djvs/nec-pc-8801-linear/IMG_20210819_163000.jpg

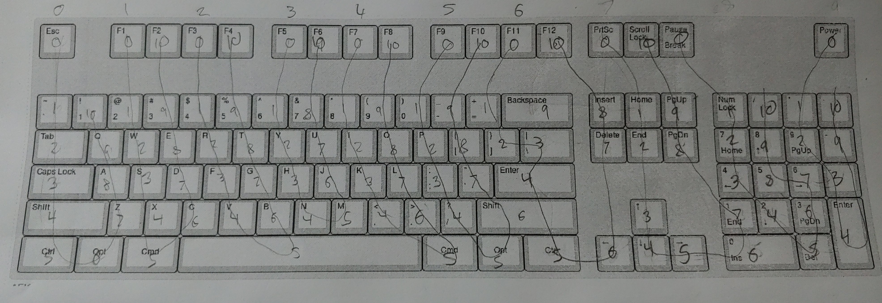
IMG_20210819_163000.jpg
