djvs/nec-pc-8801-linear/necpc8801l.kicad_sch

## KiCad design necpc8801l.kicad_sch (2022-12-16)

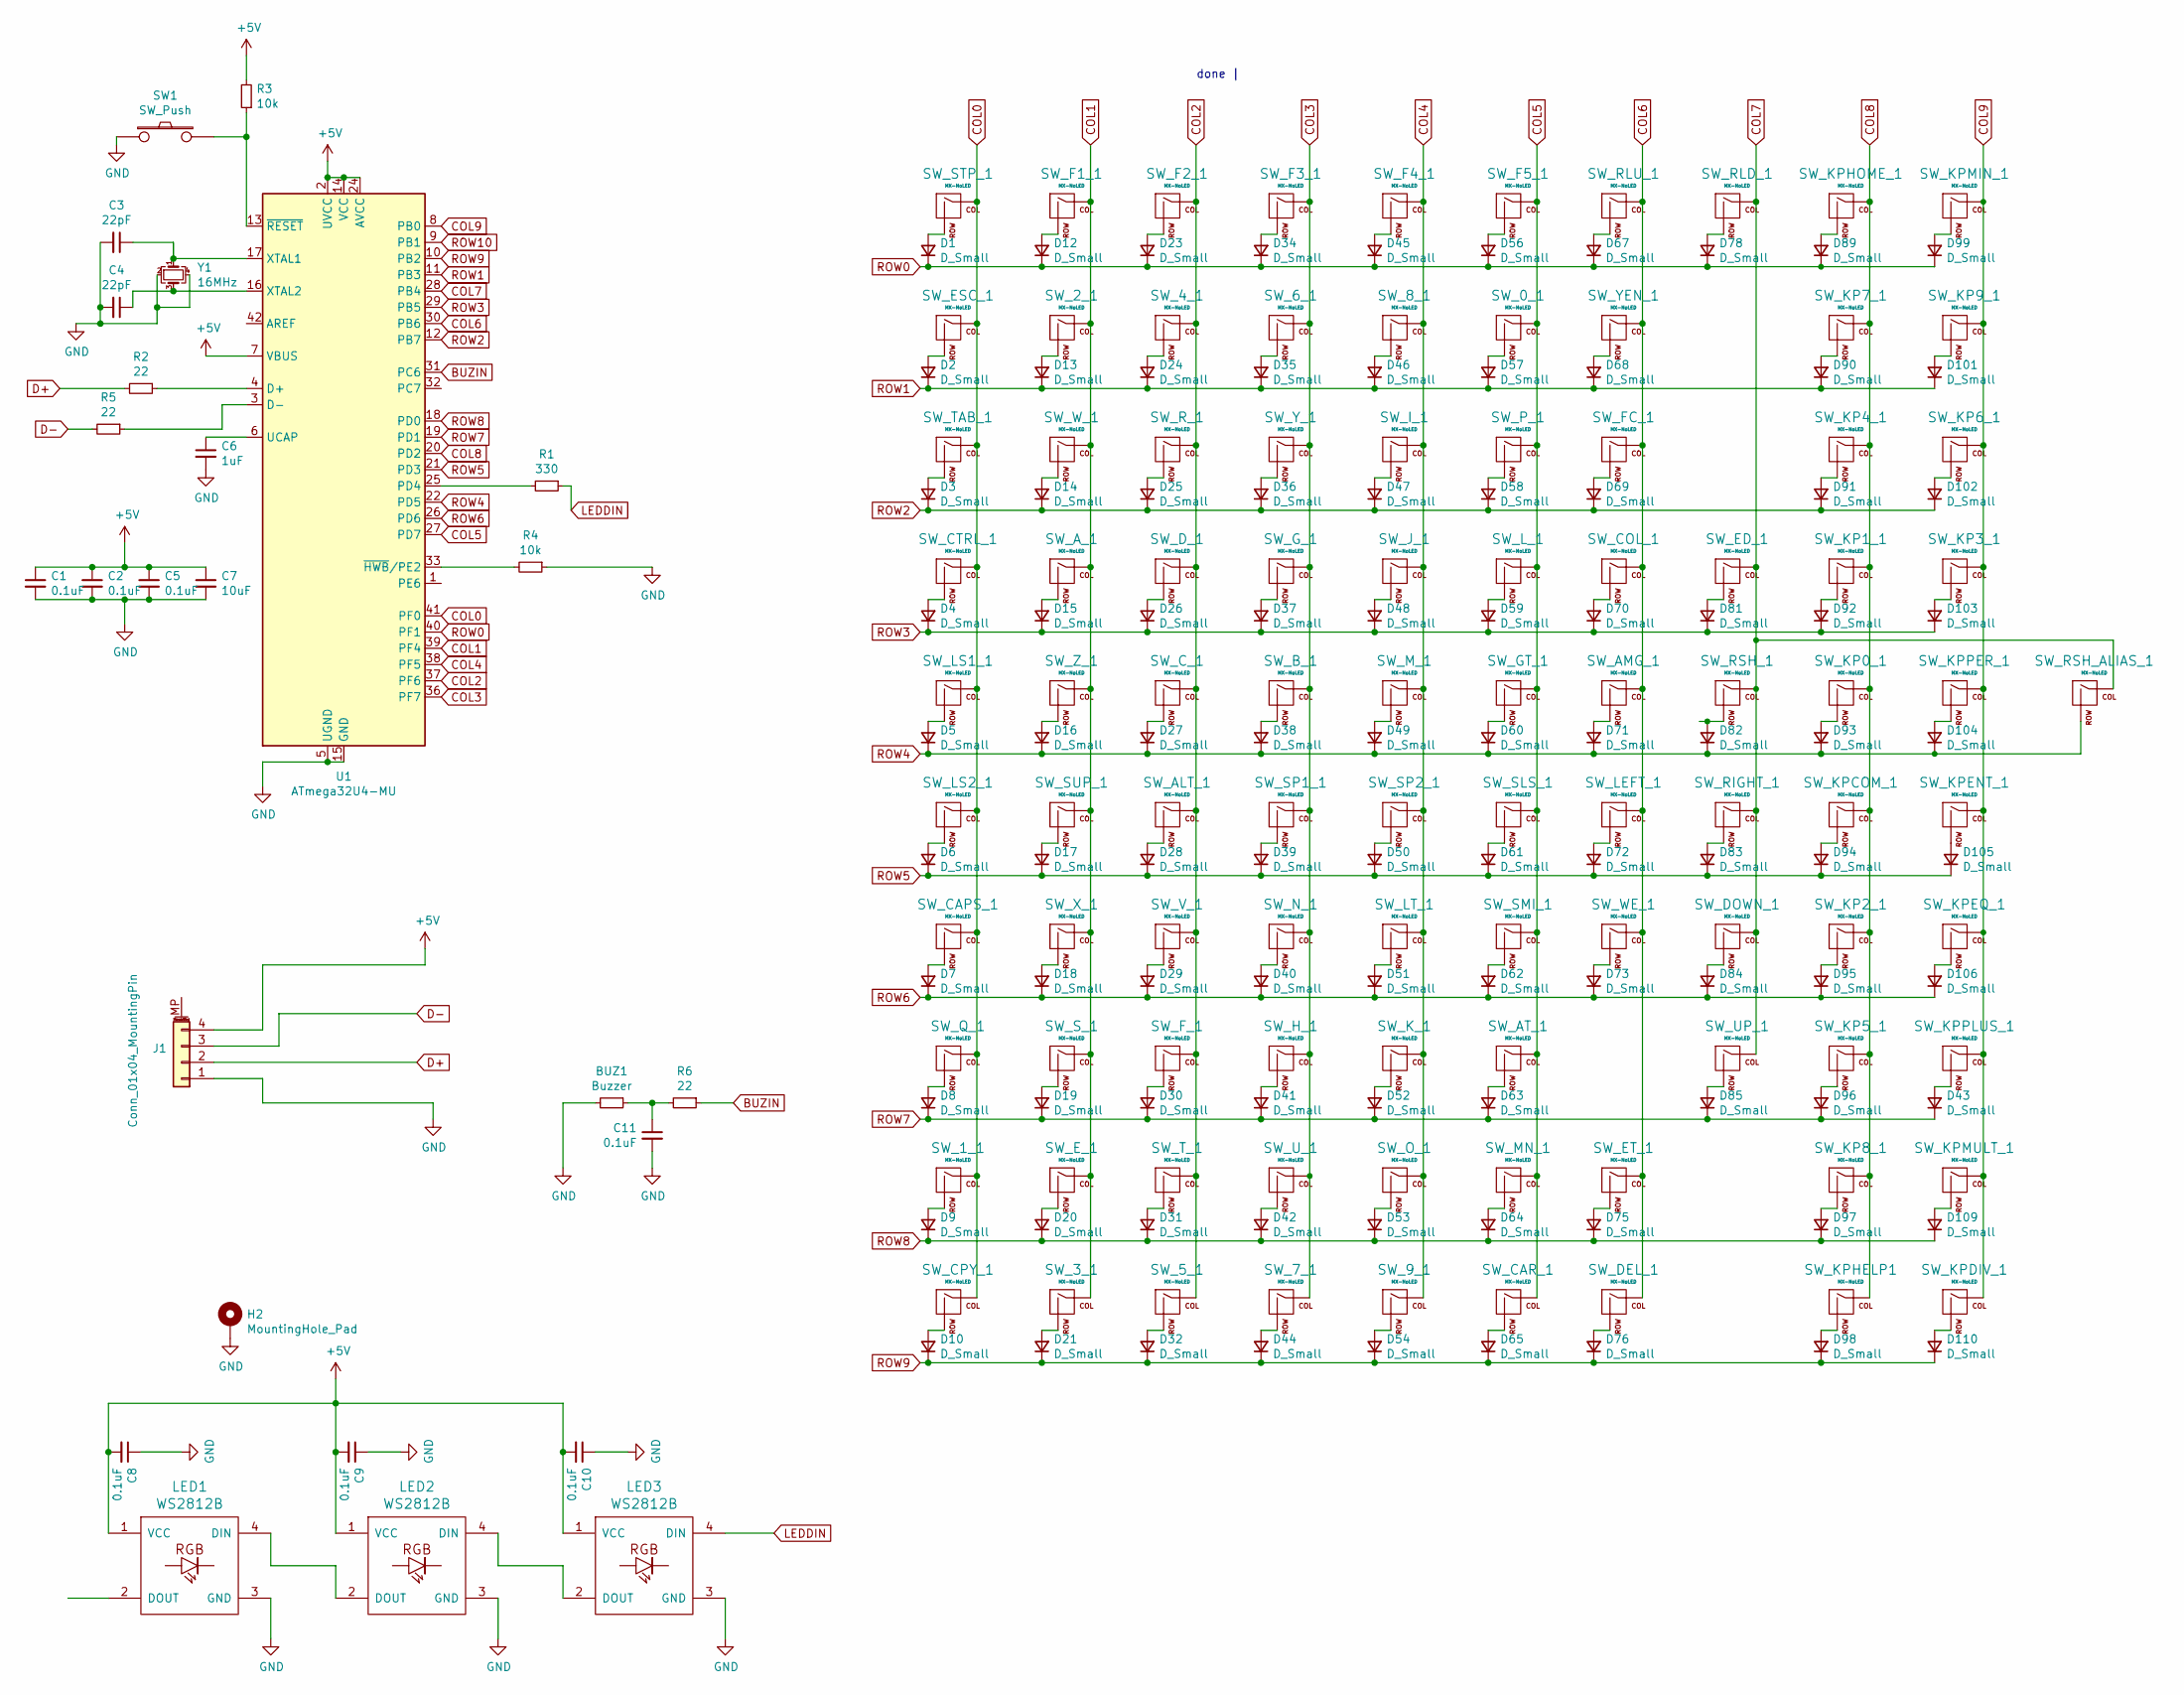
[picture p9: schematic necpc8801l.kicad_sch]

Parts:
BUZ1: Buzzer; Buzzer_Mallory_AST1109MLTRQ
C1, C2, C5, C8, C9, C10, C11: 0.1uF; C_0805_2012Metric
C3, C4: 22pF; C_0805_2012Metric
C6: 1uF; C_0805_2012Metric
C7: 10uF; C_0805_2012Metric
D1, D2, D3, D4, D5, D6, D7, D8, D9, D10, D12, D13, D14, D15, D16, D17, D18, D19, D20, D21, D23, D24, D25, D26, D27, D28, D29, D30, D31, D32, D34, D35, D36, D37, D38, D39, D40, D41, D42, D43, D44, D45, D46, D47, D48, D49, D50, D51, D52, D53, D54, D56, D57, D58, D59, D60, D61, D62, D63, D64, D65, D67, D68, D69, D70, D71, D72, D73, D75, D76, D78, D81, D82, D83, D84, D85, D89, D90, D91, D92, D93, D94, D95, D96, D97, D98, D99, D101, D102, D103, D104, D105, D106, D109, D110: D_Small; D_SOD-123
H2: MountingHole_Pad; MountingHole_2.7mm_M2.5_Pad
J1: Conn_01x04_MountingPin; JST_SH_SM04B-SRSS-TB_1x04-1MP_P1.00mm_Horizontal
LED1, LED2, LED3: WS2812B; WS2812BDual
R1: 330; R_0805_2012Metric
R2, R5, R6: 22; R_0805_2012Metric
R3, R4: 10k; R_0805_2012Metric
SW1: SW_Push; SKQG-1155865
SW_0_1, SW_1_1, SW_2_1, SW_3_1, SW_4_1, SW_5_1, SW_6_1, SW_7_1, SW_8_1, SW_9_1: MX-NoLED; mx-nec-alps
SW_ALT_1: MX-NoLED; mx-nec-alps
SW_AMG_1: MX-NoLED; mx-nec-alps
SW_AT_1: MX-NoLED; mx-nec-alps
SW_A_1: MX-NoLED; mx-nec-alps
SW_B_1: MX-NoLED; mx-nec-alps
SW_CAPS_1: MX-NoLED; mx-nec-alps
SW_CAR_1: MX-NoLED; mx-nec-alps
SW_COL_1: MX-NoLED; mx-nec-alps
SW_CPY_1: MX-NoLED; mx-nec-alps
SW_CTRL_1: MX-NoLED; mx-nec-alps
SW_C_1: MX-NoLED; mx-nec-alps
SW_DEL_1: MX-NoLED; mx-nec-alps
SW_DOWN_1: MX-NoLED; mx-nec-alps
SW_D_1: MX-NoLED; mx-nec-alps
SW_ED_1: MX-NoLED; mx-nec-alps
SW_ESC_1: MX-NoLED; mx-nec-alps
SW_ET_1: MX-NoLED; mx-nec-alps
SW_E_1: MX-NoLED; mx-nec-alps
SW_F1_1, SW_F2_1, SW_F3_1, SW_F4_1, SW_F5_1: MX-NoLED; mx-nec-alps
SW_FC_1: MX-NoLED; mx-nec-alps
SW_F_1: MX-NoLED; mx-nec-alps
SW_GT_1: MX-NoLED; mx-nec-alps
SW_G_1: MX-NoLED; mx-nec-alps
SW_H_1: MX-NoLED; mx-nec-alps
SW_I_1: MX-NoLED; mx-nec-alps
SW_J_1: MX-NoLED; mx-nec-alps
SW_KP0_1, SW_KP1_1, SW_KP2_1, SW_KP3_1, SW_KP4_1, SW_KP5_1, SW_KP6_1, SW_KP7_1, SW_KP8_1, SW_KP9_1: MX-NoLED; mx-nec-alps
SW_KPCOM_1: MX-NoLED; mx-nec-alps
SW_KPDIV_1: MX-NoLED; mx-nec-alps
SW_KPENT_1: MX-NoLED; mx-nec-alps
SW_KPEQ_1: MX-NoLED; mx-nec-alps
SW_KPHELP1: MX-NoLED; mx-nec-alps
SW_KPHOME_1: MX-NoLED; mx-nec-alps
SW_KPMIN_1: MX-NoLED; mx-nec-alps
SW_KPMULT_1: MX-NoLED; mx-nec-alps
SW_KPPER_1: MX-NoLED; mx-nec-alps
SW_KPPLUS_1: MX-NoLED; mx-nec-alps
SW_K_1: MX-NoLED; mx-nec-alps
SW_LEFT_1: MX-NoLED; mx-nec-alps
SW_LS1_1, SW_LS2_1: MX-NoLED; mx-nec-alps
SW_LT_1: MX-NoLED; mx-nec-alps
SW_L_1: MX-NoLED; mx-nec-alps
SW_MN_1: MX-NoLED; mx-nec-alps
SW_M_1: MX-NoLED; mx-nec-alps
SW_N_1: MX-NoLED; mx-nec-alps
SW_O_1: MX-NoLED; mx-nec-alps
SW_P_1: MX-NoLED; mx-nec-alps
SW_Q_1: MX-NoLED; mx-nec-alps
SW_RIGHT_1: MX-NoLED; mx-nec-alps
SW_RLD_1: MX-NoLED; mx-nec-alps
SW_RLU_1: MX-NoLED; mx-nec-alps
SW_RSH_1: MX-NoLED; mx-nec-alps
SW_RSH_ALIAS_1: MX-NoLED; mx-nec-alps
SW_R_1: MX-NoLED; mx-nec-alps
SW_SLS_1: MX-NoLED; mx-nec-alps
SW_SMI_1: MX-NoLED; mx-nec-alps
SW_SP1_1, SW_SP2_1: MX-NoLED; mx-nec-alps
SW_STP_1: MX-NoLED; mx-nec-alps
SW_SUP_1: MX-NoLED; mx-nec-alps
SW_S_1: MX-NoLED; mx-nec-alps
SW_TAB_1: MX-NoLED; mx-nec-alps
SW_T_1: MX-NoLED; mx-nec-alps
SW_UP_1: MX-NoLED; mx-nec-alps
SW_U_1: MX-NoLED; mx-nec-alps
SW_V_1: MX-NoLED; mx-nec-alps
SW_WE_1: MX-NoLED; mx-nec-alps
SW_W_1: MX-NoLED; mx-nec-alps
SW_X_1: MX-NoLED; mx-nec-alps
SW_YEN_1: MX-NoLED; mx-nec-alps
SW_Y_1: MX-NoLED; mx-nec-alps
SW_Z_1: MX-NoLED; mx-nec-alps
U1: ATmega32U4-MU; atmega32u4-mu-and-au
Y1: 16MHz; Crystal_SMD_3225-4Pin_3.2x2.5mm

Connections:
+5V: C1.1, C2.1, C5.1, C7.1, C8.2, C9.2, C10.2, J1.4, LED1.1 (VCC), LED2.1 (VCC), LED3.1 (VCC), R3.2, U1.2 (UVCC), U1.7 (VBUS), U1.14 (VCC), U1.24 (AVCC), U1.34 (VCC), U1.44 (AVCC)
BUZIN: R6.1, U1.31 (PC6)
COL0: SW_1_1.1 (COL), SW_CAPS_1.1 (COL), SW_CPY_1.1 (COL), SW_CTRL_1.1 (COL), SW_ESC_1.1 (COL), SW_LS1_1.1 (COL), SW_LS2_1.1 (COL), SW_Q_1.1 (COL), SW_STP_1.1 (COL), SW_TAB_1.1 (COL), U1.41 (PF0)
COL1: SW_2_1.1 (COL), SW_3_1.1 (COL), SW_A_1.1 (COL), SW_E_1.1 (COL), SW_F1_1.1 (COL), SW_SUP_1.1 (COL), SW_S_1.1 (COL), SW_W_1.1 (COL), SW_X_1.1 (COL), SW_Z_1.1 (COL), U1.39 (PF4)
COL2: SW_4_1.1 (COL), SW_5_1.1 (COL), SW_ALT_1.1 (COL), SW_C_1.1 (COL), SW_D_1.1 (COL), SW_F2_1.1 (COL), SW_F_1.1 (COL), SW_R_1.1 (COL), SW_T_1.1 (COL), SW_V_1.1 (COL), U1.37 (PF6)
COL3: SW_6_1.1 (COL), SW_7_1.1 (COL), SW_B_1.1 (COL), SW_F3_1.1 (COL), SW_G_1.1 (COL), SW_H_1.1 (COL), SW_N_1.1 (COL), SW_SP1_1.1 (COL), SW_U_1.1 (COL), SW_Y_1.1 (COL), U1.36 (PF7)
COL4: SW_8_1.1 (COL), SW_9_1.1 (COL), SW_F4_1.1 (COL), SW_I_1.1 (COL), SW_J_1.1 (COL), SW_K_1.1 (COL), SW_LT_1.1 (COL), SW_M_1.1 (COL), SW_O_1.1 (COL), SW_SP2_1.1 (COL), U1.38 (PF5)
COL5: SW_0_1.1 (COL), SW_AT_1.1 (COL), SW_CAR_1.1 (COL), SW_F5_1.1 (COL), SW_GT_1.1 (COL), SW_L_1.1 (COL), SW_MN_1.1 (COL), SW_P_1.1 (COL), SW_SLS_1.1 (COL), SW_SMI_1.1 (COL), U1.27 (PD7)
COL6: SW_AMG_1.1 (COL), SW_COL_1.1 (COL), SW_DEL_1.1 (COL), SW_ET_1.1 (COL), SW_FC_1.1 (COL), SW_LEFT_1.1 (COL), SW_RLU_1.1 (COL), SW_WE_1.1 (COL), SW_YEN_1.1 (COL), U1.30 (PB6)
COL7: SW_DOWN_1.1 (COL), SW_ED_1.1 (COL), SW_RIGHT_1.1 (COL), SW_RLD_1.1 (COL), SW_RSH_1.1 (COL), SW_RSH_ALIAS_1.1 (COL), SW_UP_1.1 (COL), U1.28 (PB4)
COL8: SW_KP0_1.1 (COL), SW_KP1_1.1 (COL), SW_KP2_1.1 (COL), SW_KP4_1.1 (COL), SW_KP5_1.1 (COL), SW_KP7_1.1 (COL), SW_KP8_1.1 (COL), SW_KPCOM_1.1 (COL), SW_KPHELP1.1 (COL), SW_KPHOME_1.1 (COL), U1.20 (PD2)
COL9: SW_KP3_1.1 (COL), SW_KP6_1.1 (COL), SW_KP9_1.1 (COL), SW_KPDIV_1.1 (COL), SW_KPENT_1.1 (COL), SW_KPEQ_1.1 (COL), SW_KPMIN_1.1 (COL), SW_KPMULT_1.1 (COL), SW_KPPER_1.1 (COL), SW_KPPLUS_1.1 (COL), U1.8 (PB0)
D+: J1.2, R2.2
D-: J1.3, R5.2
GND: BUZ1.2, C1.2, C2.2, C3.2, C4.2, C5.2, C6.2, C7.2, C8.1, C9.1, C10.1, C11.2, H2.1, J1.1, LED1.3 (GND), LED2.3 (GND), LED3.3 (GND), R4.1, SW1.1, U1.5 (UGND), U1.15 (GND), U1.23 (GND), U1.35 (GND), U1.43 (GND), U1.45 (GND), Y1.2, Y1.4
LEDDIN: LED3.4 (DIN), R1.1
unnamed: BUZ1.1, C11.1, R6.2
unnamed: C3.1, U1.17 (XTAL1), Y1.1
unnamed: C4.1, U1.16 (XTAL2), Y1.3
unnamed: C6.1, U1.6 (UCAP)
unnamed: D1.2 (A), SW_STP_1.2 (ROW)
unnamed: D2.2 (A), SW_ESC_1.2 (ROW)
unnamed: D3.2 (A), SW_TAB_1.2 (ROW)
unnamed: D4.2 (A), SW_CTRL_1.2 (ROW)
unnamed: D5.2 (A), SW_LS1_1.2 (ROW)
unnamed: D6.2 (A), SW_LS2_1.2 (ROW)
unnamed: D7.2 (A), SW_CAPS_1.2 (ROW)
unnamed: D8.2 (A), SW_Q_1.2 (ROW)
unnamed: D9.2 (A), SW_1_1.2 (ROW)
unnamed: D10.2 (A), SW_CPY_1.2 (ROW)
unnamed: D12.2 (A), SW_F1_1.2 (ROW)
unnamed: D13.2 (A), SW_2_1.2 (ROW)
unnamed: D14.2 (A), SW_W_1.2 (ROW)
unnamed: D15.2 (A), SW_A_1.2 (ROW)
unnamed: D16.2 (A), SW_Z_1.2 (ROW)
unnamed: D17.2 (A), SW_SUP_1.2 (ROW)
unnamed: D18.2 (A), SW_X_1.2 (ROW)
unnamed: D19.2 (A), SW_S_1.2 (ROW)
unnamed: D20.2 (A), SW_E_1.2 (ROW)
unnamed: D21.2 (A), SW_3_1.2 (ROW)
unnamed: D23.2 (A), SW_F2_1.2 (ROW)
unnamed: D24.2 (A), SW_4_1.2 (ROW)
unnamed: D25.2 (A), SW_R_1.2 (ROW)
unnamed: D26.2 (A), SW_D_1.2 (ROW)
unnamed: D27.2 (A), SW_C_1.2 (ROW)
unnamed: D28.2 (A), SW_ALT_1.2 (ROW)
unnamed: D29.2 (A), SW_V_1.2 (ROW)
unnamed: D30.2 (A), SW_F_1.2 (ROW)
unnamed: D31.2 (A), SW_T_1.2 (ROW)
unnamed: D32.2 (A), SW_5_1.2 (ROW)
unnamed: D34.2 (A), SW_F3_1.2 (ROW)
unnamed: D35.2 (A), SW_6_1.2 (ROW)
unnamed: D36.2 (A), SW_Y_1.2 (ROW)
unnamed: D37.2 (A), SW_G_1.2 (ROW)
unnamed: D38.2 (A), SW_B_1.2 (ROW)
unnamed: D39.2 (A), SW_SP1_1.2 (ROW)
unnamed: D40.2 (A), SW_N_1.2 (ROW)
unnamed: D41.2 (A), SW_H_1.2 (ROW)
unnamed: D42.2 (A), SW_U_1.2 (ROW)
unnamed: D43.2 (A), SW_KPPLUS_1.2 (ROW)
unnamed: D44.2 (A), SW_7_1.2 (ROW)
unnamed: D45.2 (A), SW_F4_1.2 (ROW)
unnamed: D46.2 (A), SW_8_1.2 (ROW)
unnamed: D47.2 (A), SW_I_1.2 (ROW)
unnamed: D48.2 (A), SW_J_1.2 (ROW)
unnamed: D49.2 (A), SW_M_1.2 (ROW)
unnamed: D50.2 (A), SW_SP2_1.2 (ROW)
unnamed: D51.2 (A), SW_LT_1.2 (ROW)
unnamed: D52.2 (A), SW_K_1.2 (ROW)
unnamed: D53.2 (A), SW_O_1.2 (ROW)
unnamed: D54.2 (A), SW_9_1.2 (ROW)
unnamed: D56.2 (A), SW_F5_1.2 (ROW)
unnamed: D57.2 (A), SW_0_1.2 (ROW)
unnamed: D58.2 (A), SW_P_1.2 (ROW)
unnamed: D59.2 (A), SW_L_1.2 (ROW)
unnamed: D60.2 (A), SW_GT_1.2 (ROW)
unnamed: D61.2 (A), SW_SLS_1.2 (ROW)
unnamed: D62.2 (A), SW_SMI_1.2 (ROW)
unnamed: D63.2 (A), SW_AT_1.2 (ROW)
unnamed: D64.2 (A), SW_MN_1.2 (ROW)
unnamed: D65.2 (A), SW_CAR_1.2 (ROW)
unnamed: D67.2 (A), SW_RLU_1.2 (ROW)
unnamed: D68.2 (A), SW_YEN_1.2 (ROW)
unnamed: D69.2 (A), SW_FC_1.2 (ROW)
unnamed: D70.2 (A), SW_COL_1.2 (ROW)
unnamed: D71.2 (A), SW_AMG_1.2 (ROW)
unnamed: D72.2 (A), SW_LEFT_1.2 (ROW)
unnamed: D73.2 (A), SW_WE_1.2 (ROW)
unnamed: D75.2 (A), SW_ET_1.2 (ROW)
unnamed: D76.2 (A), SW_DEL_1.2 (ROW)
unnamed: D78.2 (A), SW_RLD_1.2 (ROW)
unnamed: D81.2 (A), SW_ED_1.2 (ROW)
unnamed: D82.2 (A), SW_RSH_1.2 (ROW)
unnamed: D83.2 (A), SW_RIGHT_1.2 (ROW)
unnamed: D84.2 (A), SW_DOWN_1.2 (ROW)
unnamed: D85.2 (A), SW_UP_1.2 (ROW)
unnamed: D89.2 (A), SW_KPHOME_1.2 (ROW)
unnamed: D90.2 (A), SW_KP7_1.2 (ROW)
unnamed: D91.2 (A), SW_KP4_1.2 (ROW)
unnamed: D92.2 (A), SW_KP1_1.2 (ROW)
unnamed: D93.2 (A), SW_KP0_1.2 (ROW)
unnamed: D94.2 (A), SW_KPCOM_1.2 (ROW)
unnamed: D95.2 (A), SW_KP2_1.2 (ROW)
unnamed: D96.2 (A), SW_KP5_1.2 (ROW)
unnamed: D97.2 (A), SW_KP8_1.2 (ROW)
unnamed: D98.2 (A), SW_KPHELP1.2 (ROW)
unnamed: D99.2 (A), SW_KPMIN_1.2 (ROW)
unnamed: D101.2 (A), SW_KP9_1.2 (ROW)
unnamed: D102.2 (A), SW_KP6_1.2 (ROW)
unnamed: D103.2 (A), SW_KP3_1.2 (ROW)
unnamed: D104.2 (A), SW_KPPER_1.2 (ROW)
unnamed: D105.2 (A), SW_KPENT_1.2 (ROW)
unnamed: D106.2 (A), SW_KPEQ_1.2 (ROW)
unnamed: D109.2 (A), SW_KPMULT_1.2 (ROW)
unnamed: D110.2 (A), SW_KPDIV_1.2 (ROW)
unnamed: LED1.4 (DIN), LED2.2 (DOUT)
unnamed: LED2.4 (DIN), LED3.2 (DOUT)
unnamed: R1.2, U1.25 (PD4)
unnamed: R2.1, U1.4 (D+)
unnamed: R3.1, SW1.2, U1.13 (~RESET)
unnamed: R4.2, U1.33 (~HWB/PE2)
unnamed: R5.1, U1.3 (D-)
ROW0: D1.1 (K), D12.1 (K), D23.1 (K), D34.1 (K), D45.1 (K), D56.1 (K), D67.1 (K), D78.1 (K), D89.1 (K), D99.1 (K), U1.40 (PF1)
ROW1: D2.1 (K), D13.1 (K), D24.1 (K), D35.1 (K), D46.1 (K), D57.1 (K), D68.1 (K), D90.1 (K), D101.1 (K), U1.11 (PB3)
ROW2: D3.1 (K), D14.1 (K), D25.1 (K), D36.1 (K), D47.1 (K), D58.1 (K), D69.1 (K), D91.1 (K), D102.1 (K), U1.12 (PB7)
ROW3: D4.1 (K), D15.1 (K), D26.1 (K), D37.1 (K), D48.1 (K), D59.1 (K), D70.1 (K), D81.1 (K), D92.1 (K), D103.1 (K), U1.29 (PB5)
ROW4: D5.1 (K), D16.1 (K), D27.1 (K), D38.1 (K), D49.1 (K), D60.1 (K), D71.1 (K), D82.1 (K), D93.1 (K), D104.1 (K), SW_RSH_ALIAS_1.2 (ROW), U1.22 (PD5)
ROW5: D6.1 (K), D17.1 (K), D28.1 (K), D39.1 (K), D50.1 (K), D61.1 (K), D72.1 (K), D83.1 (K), D94.1 (K), D105.1 (K), U1.21 (PD3)
ROW6: D7.1 (K), D18.1 (K), D29.1 (K), D40.1 (K), D51.1 (K), D62.1 (K), D73.1 (K), D84.1 (K), D95.1 (K), D106.1 (K), U1.26 (PD6)
ROW7: D8.1 (K), D19.1 (K), D30.1 (K), D41.1 (K), D43.1 (K), D52.1 (K), D63.1 (K), D85.1 (K), D96.1 (K), U1.19 (PD1)
ROW8: D9.1 (K), D20.1 (K), D31.1 (K), D42.1 (K), D53.1 (K), D64.1 (K), D75.1 (K), D97.1 (K), D109.1 (K), U1.18 (PD0)
ROW9: D10.1 (K), D21.1 (K), D32.1 (K), D44.1 (K), D54.1 (K), D65.1 (K), D76.1 (K), D98.1 (K), D110.1 (K), U1.10 (PB2)
ROW10: U1.9 (PB1)

Notes on the sheet:
done |
